drivera02Dev/EE418-FMCW-Radar/SPI/04b_MADV.jpg

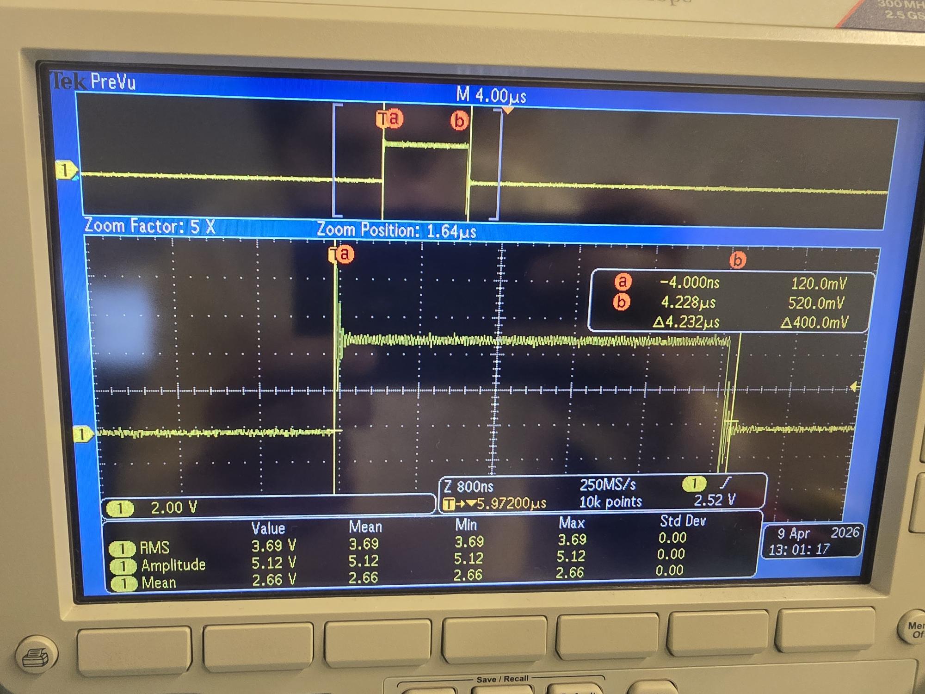
SPI/04b_MADV.jpg
