drivera02Dev/EE418-FMCW-Radar/SPI/Read_1.jpg

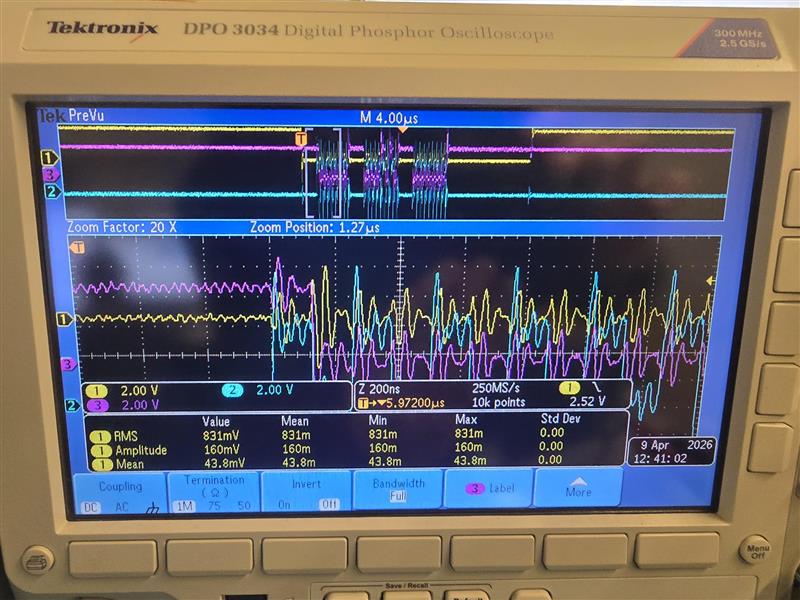
SPI/Read_1.jpg
