drivera02Dev/EE418-FMCW-Radar/SPI/Read_2.jpg

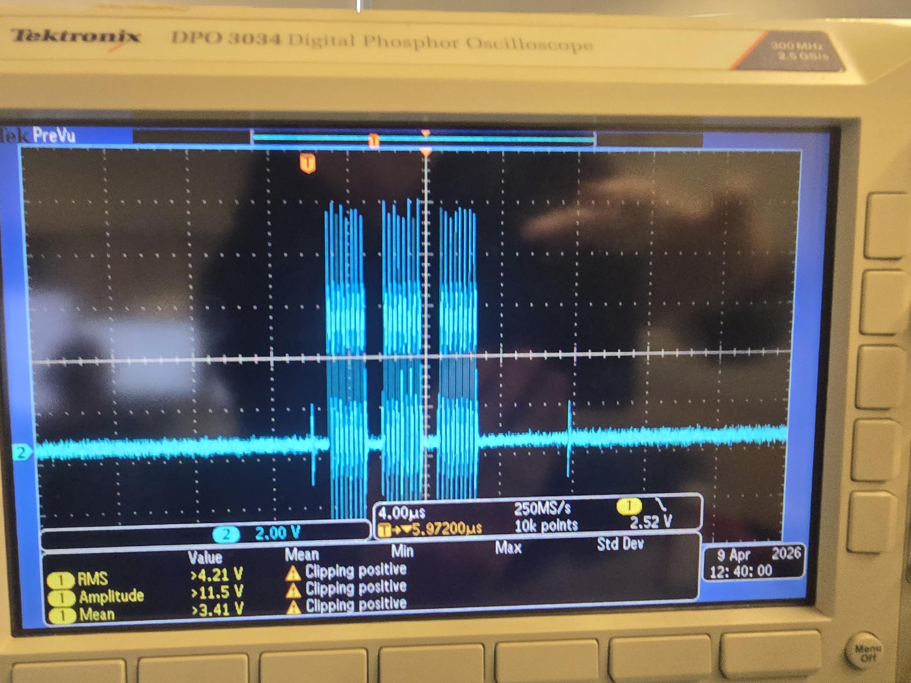
SPI/Read_2.jpg
