drivera02Dev/EE418-FMCW-Radar/SPI/Read_3.jpg

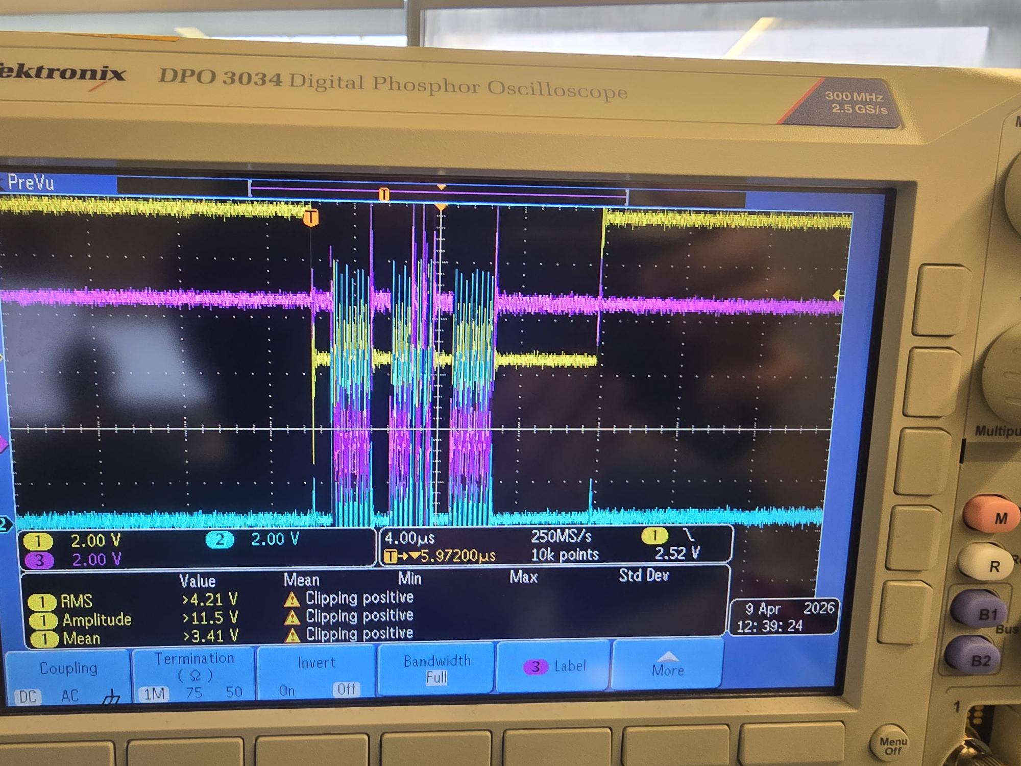
SPI/Read_3.jpg
