drivera02Dev/EE418-FMCW-Radar/SPI/Read_5.jpg

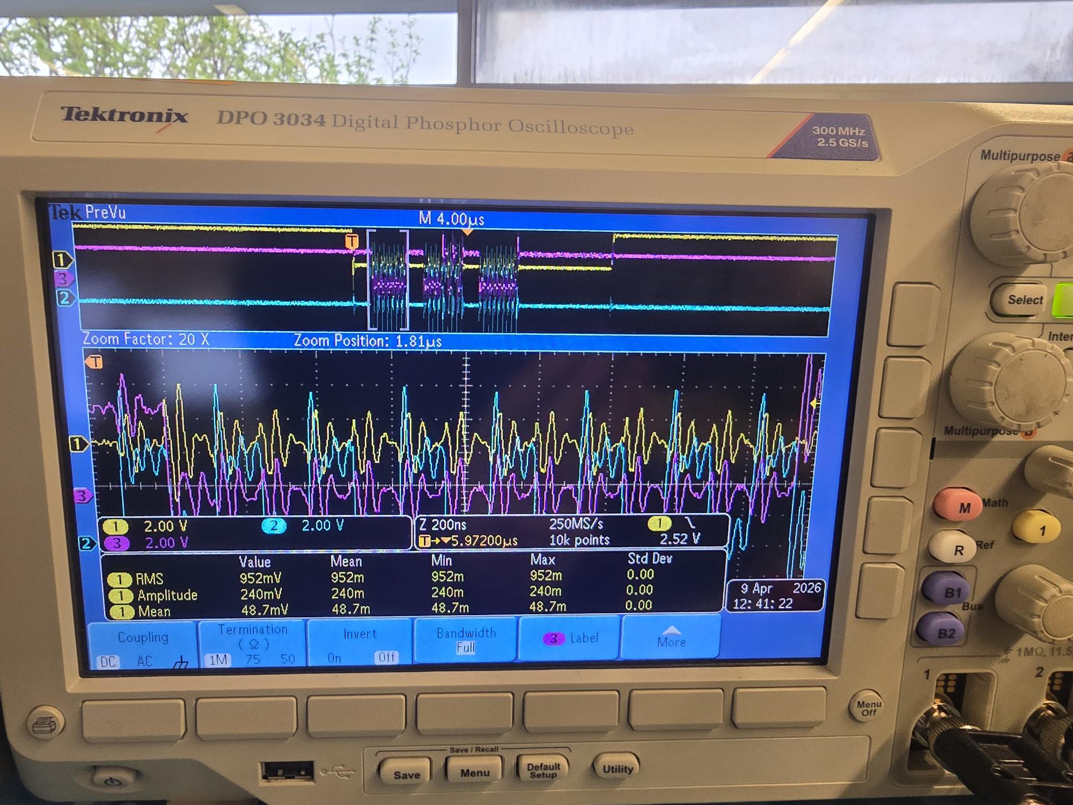
SPI/Read_5.jpg
