drivera02Dev/EE418-FMCW-Radar/SPI/Read_6.jpg

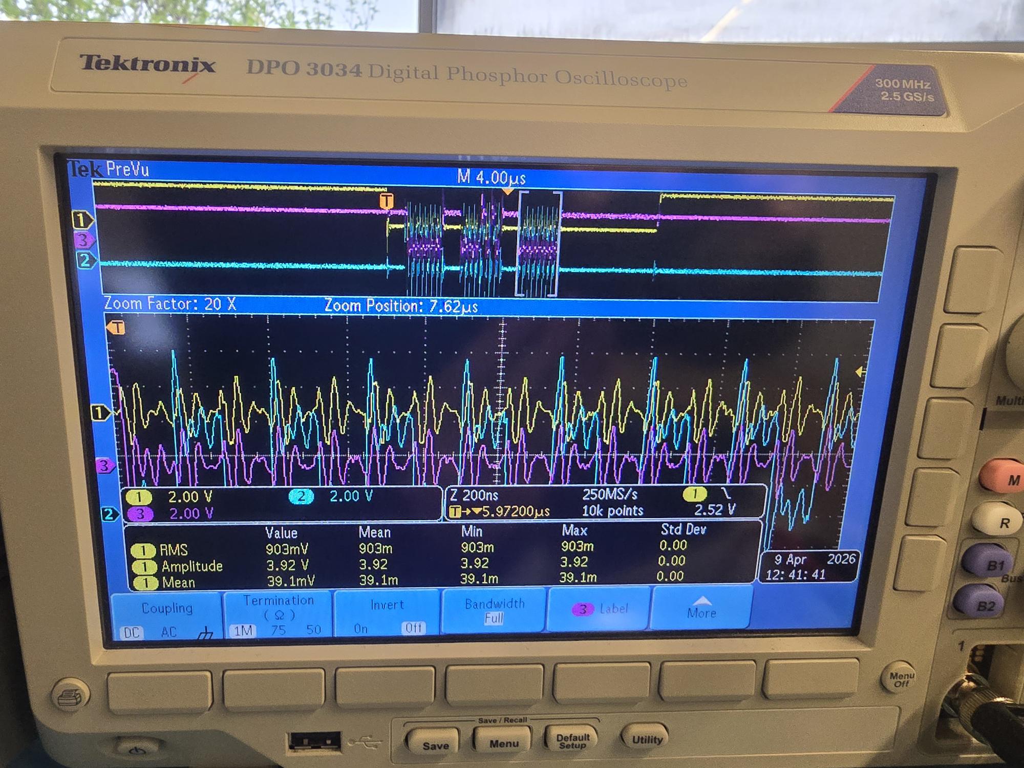
SPI/Read_6.jpg
