drivera02Dev/EE418-FMCW-Radar/SPI/Read_7.jpg

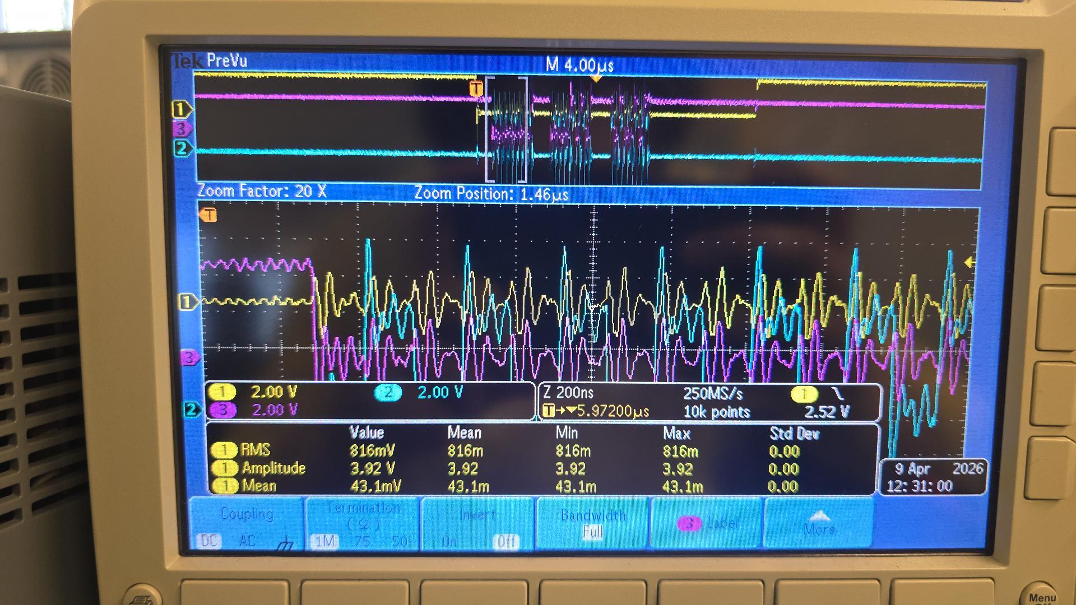
SPI/Read_7.jpg
