drivera02Dev/EE418-FMCW-Radar/SPI/Reference_1.jpg

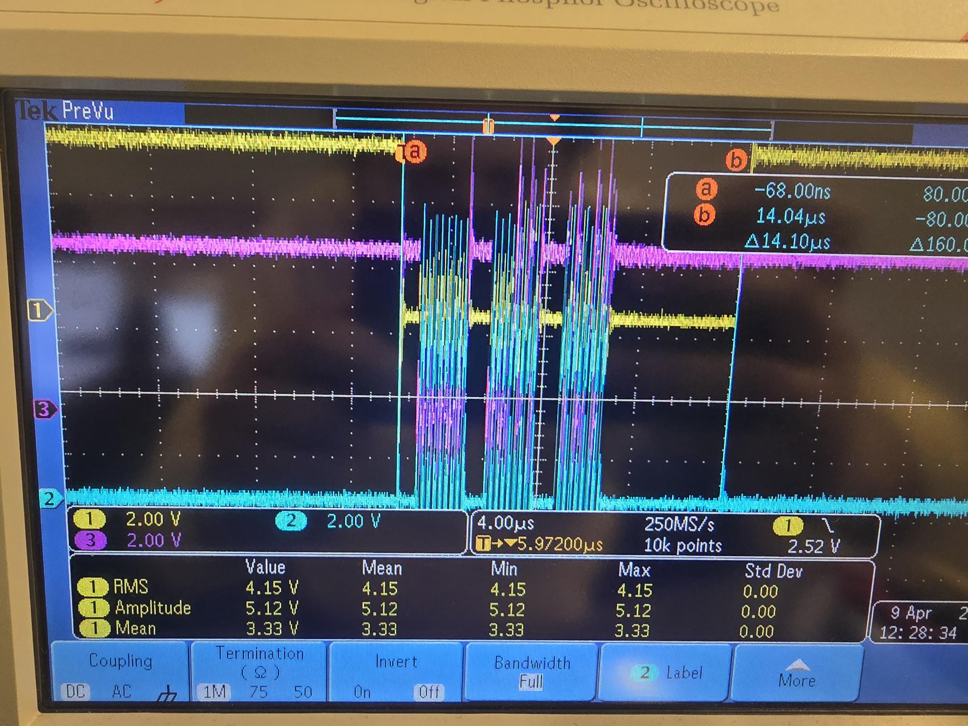
SPI/Reference_1.jpg
