drivera02Dev/EE418-FMCW-Radar/SPI/Reference_2.jpg

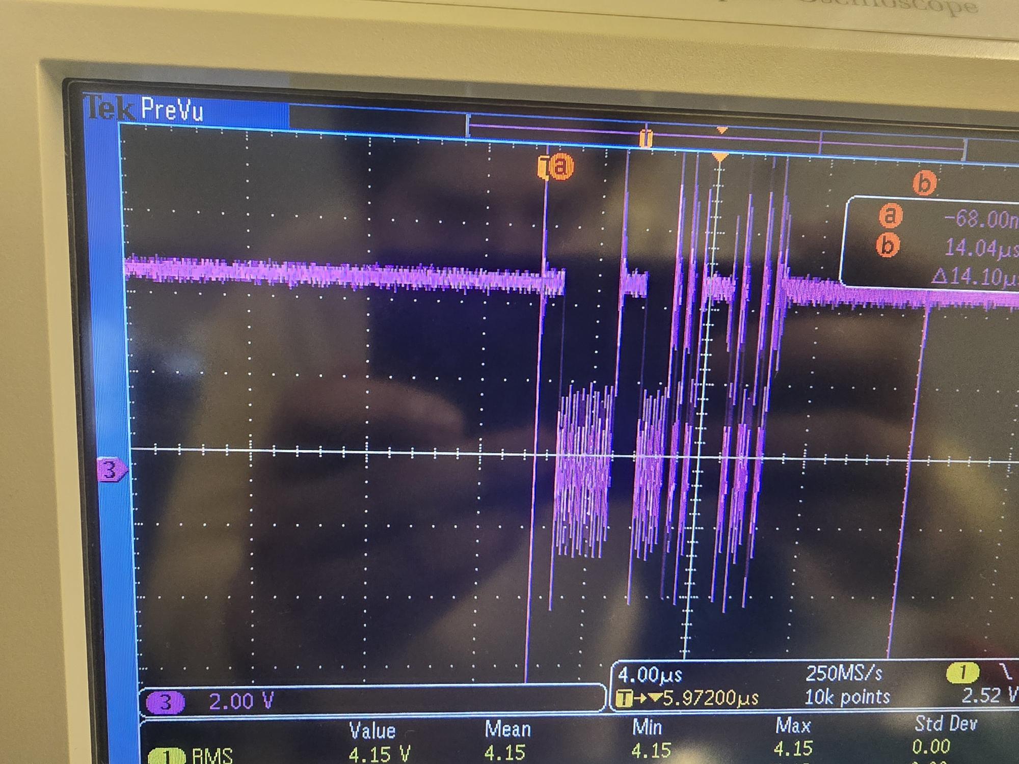
SPI/Reference_2.jpg
