drivera02Dev/EE418-FMCW-Radar/SPI/Reference_3.jpg

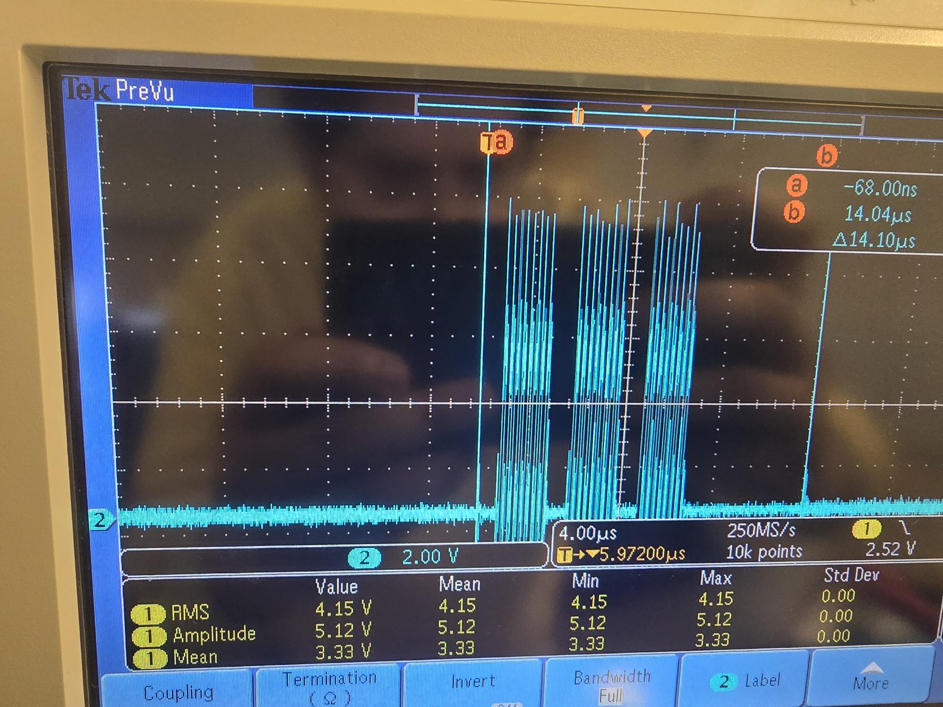
SPI/Reference_3.jpg
