drivera02Dev/EE418-FMCW-Radar/SPI/Reference_5.jpg

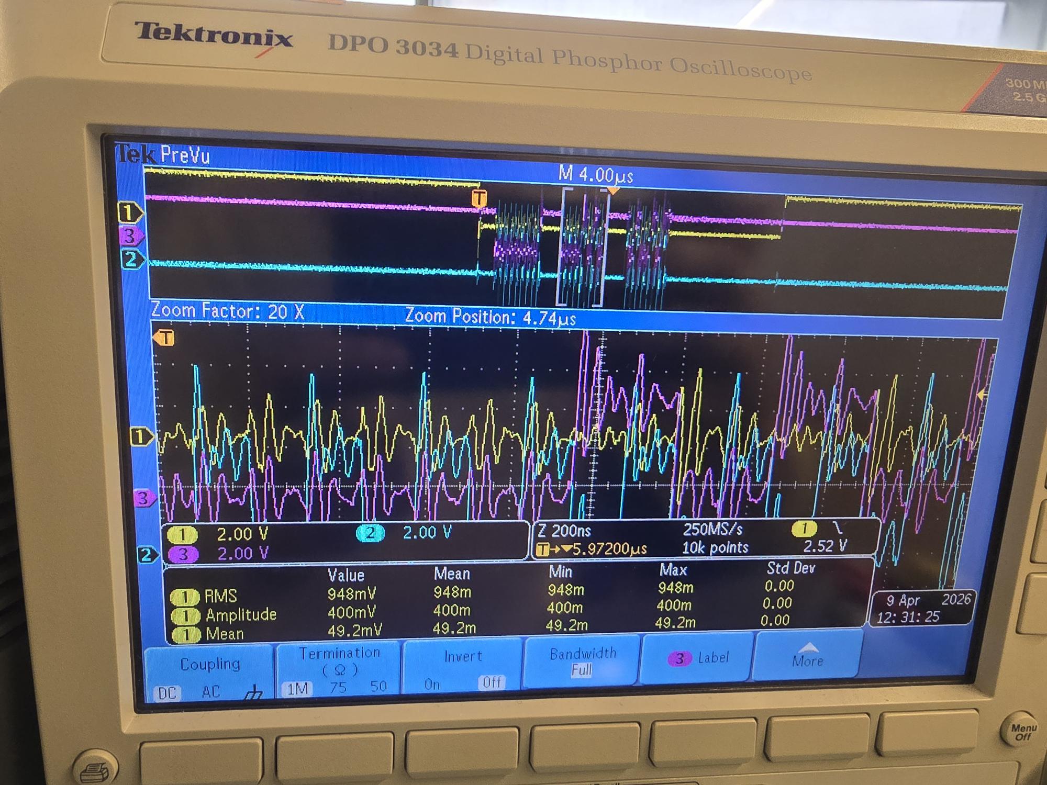
SPI/Reference_5.jpg
