drivera02Dev/EE418-FMCW-Radar/SPI/Reference_6.jpg

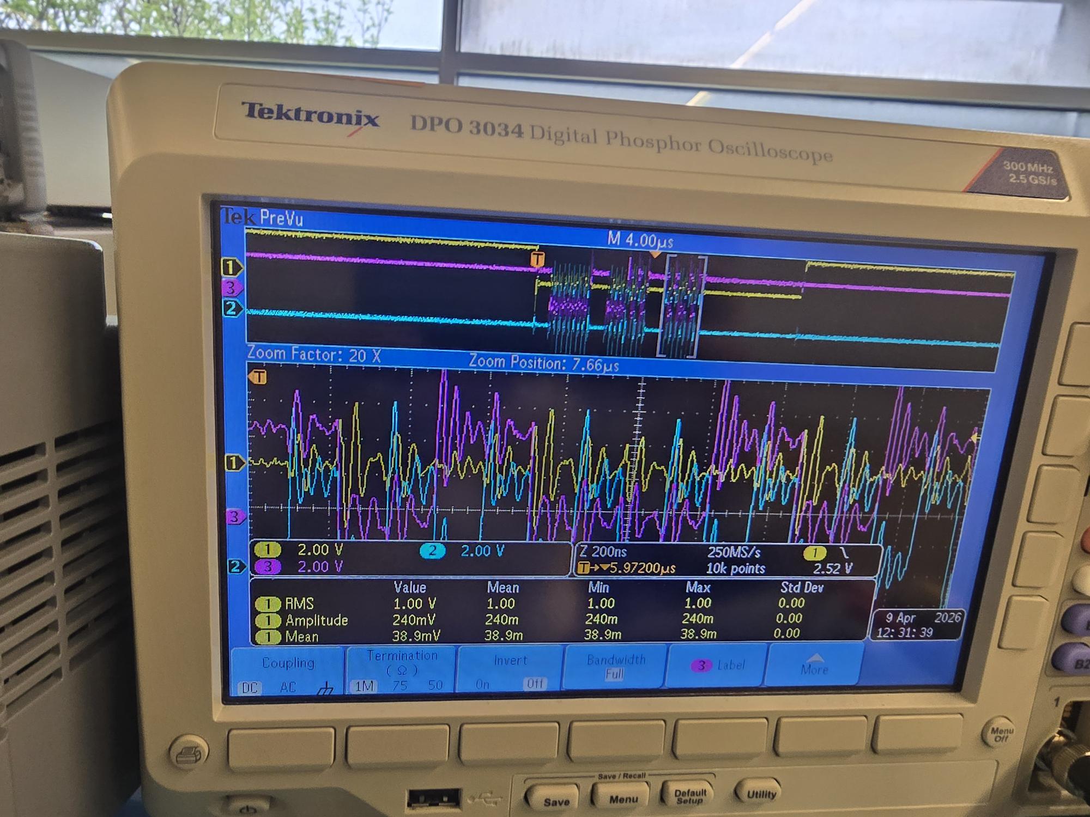
SPI/Reference_6.jpg
