drivera02Dev/EE418-FMCW-Radar/SPI/Reset_1.jpg

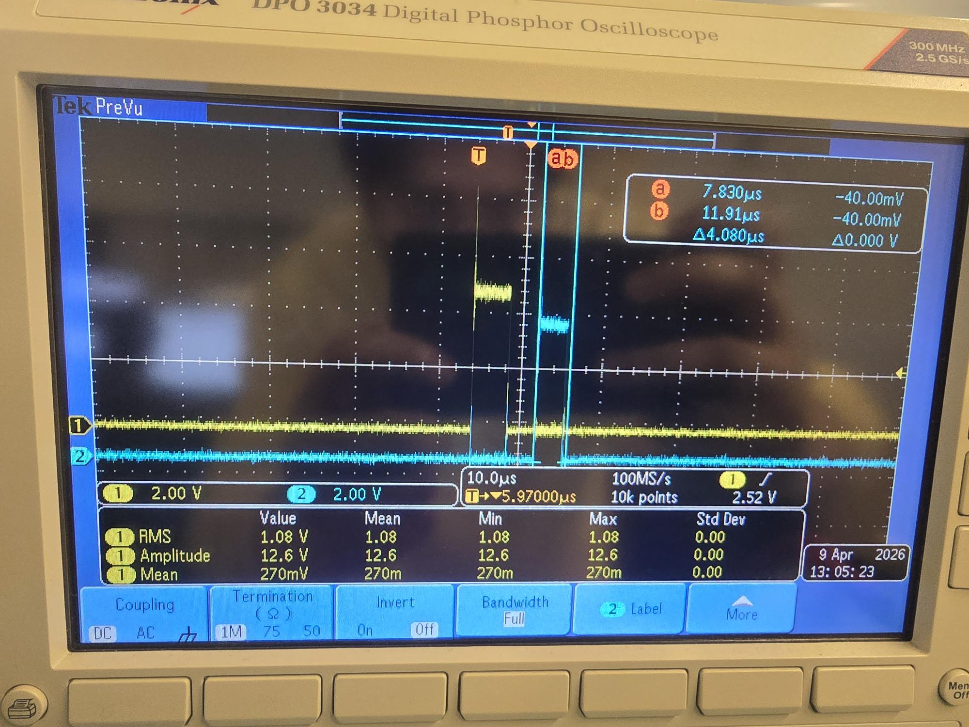
SPI/Reset_1.jpg
