drivera02Dev/EE418-FMCW-Radar/SPI/Reset_3.jpg

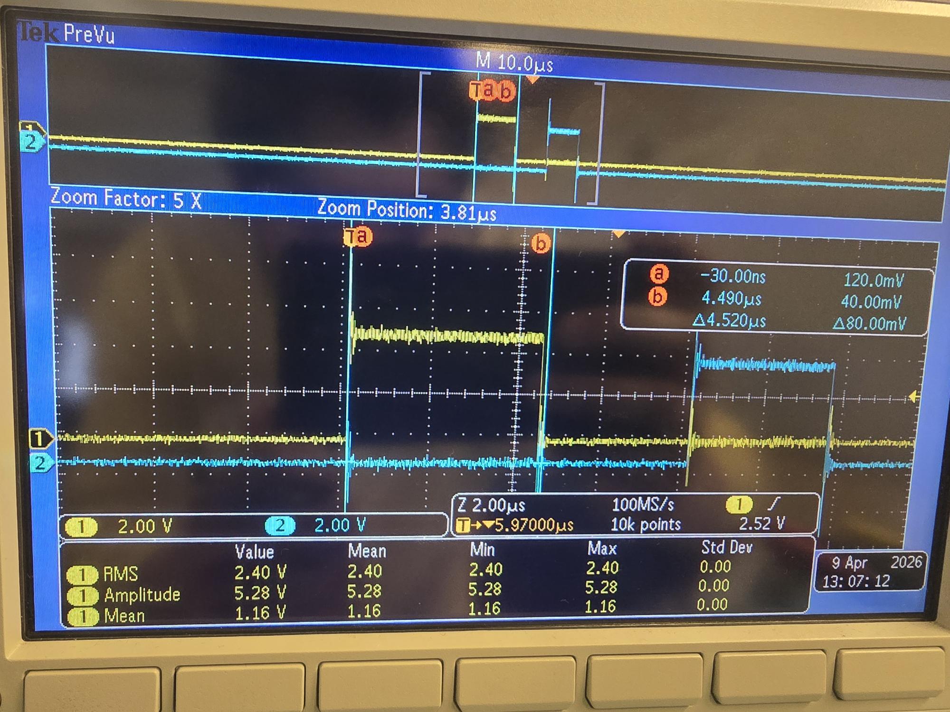
SPI/Reset_3.jpg
