drivera02Dev/EE418-FMCW-Radar/SPI/Reset_4.jpg

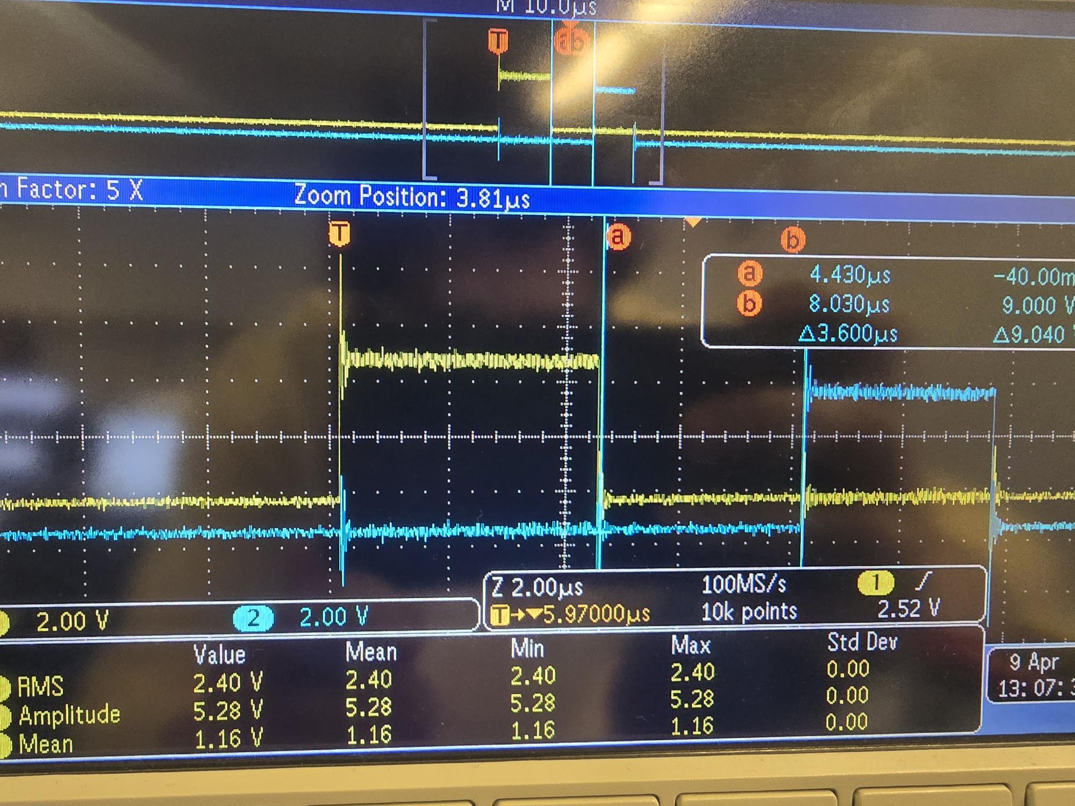
SPI/Reset_4.jpg
