drivera02Dev/EE418-FMCW-Radar/SPI/shared image (1).jpg

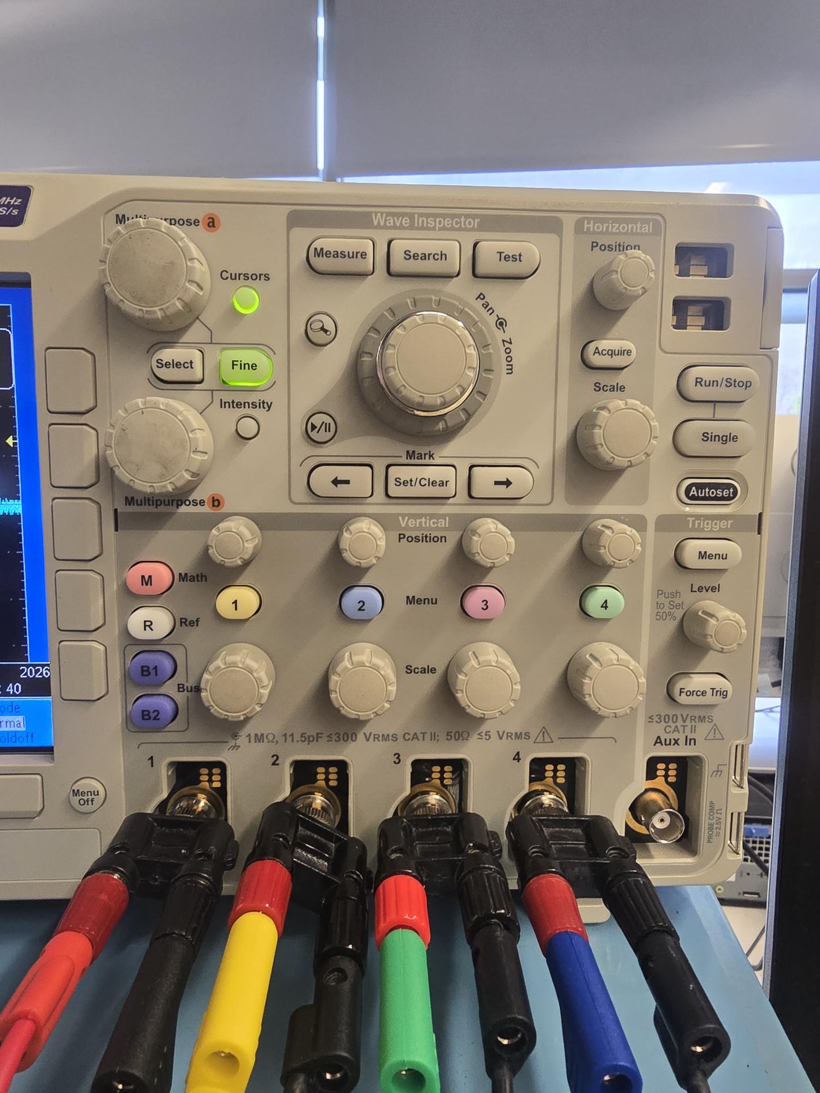
SPI/shared image (1).jpg
