drivera02Dev/EE418-FMCW-Radar/SPI/shared image (2).jpg

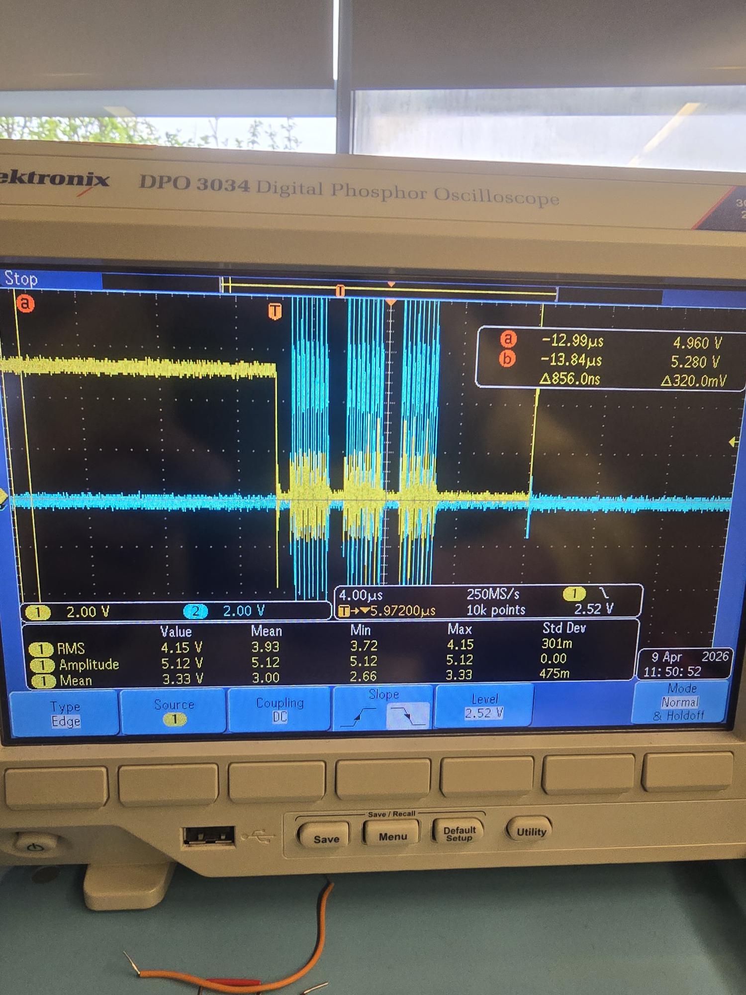
SPI/shared image (2).jpg
