drivera02Dev/EE418-FMCW-Radar/SPI/shared image (3).jpg

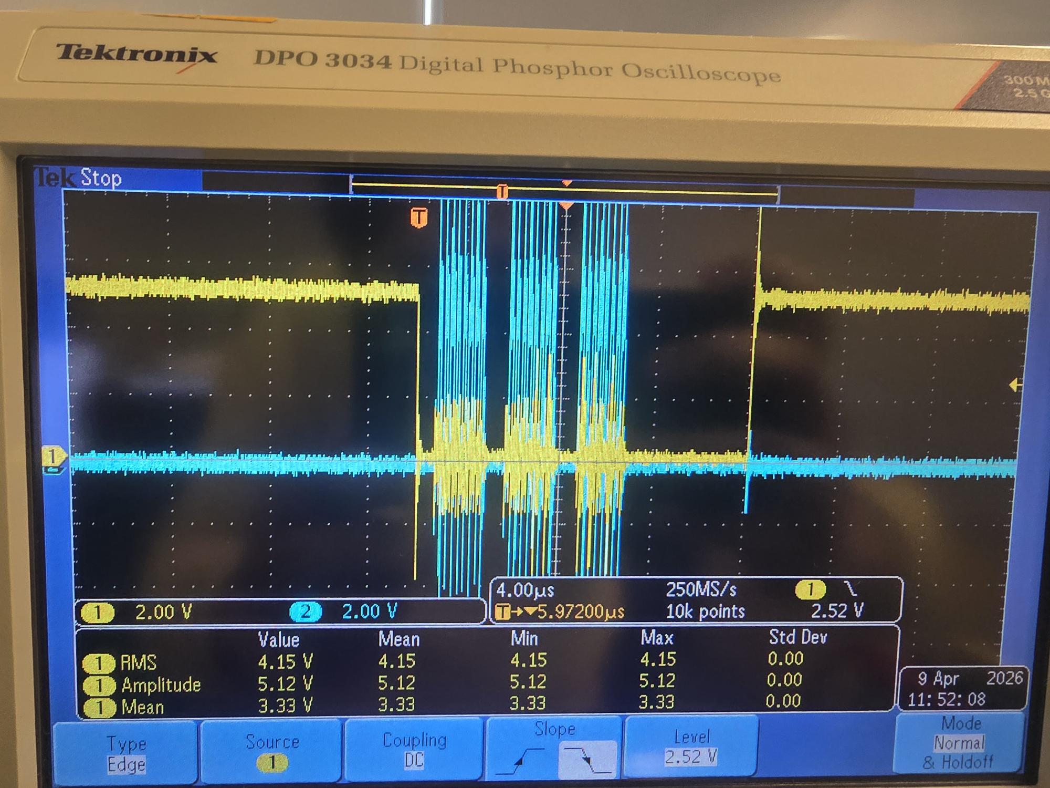
SPI/shared image (3).jpg
