drivera02Dev/EE418-FMCW-Radar/SPI/shared image (4).jpg

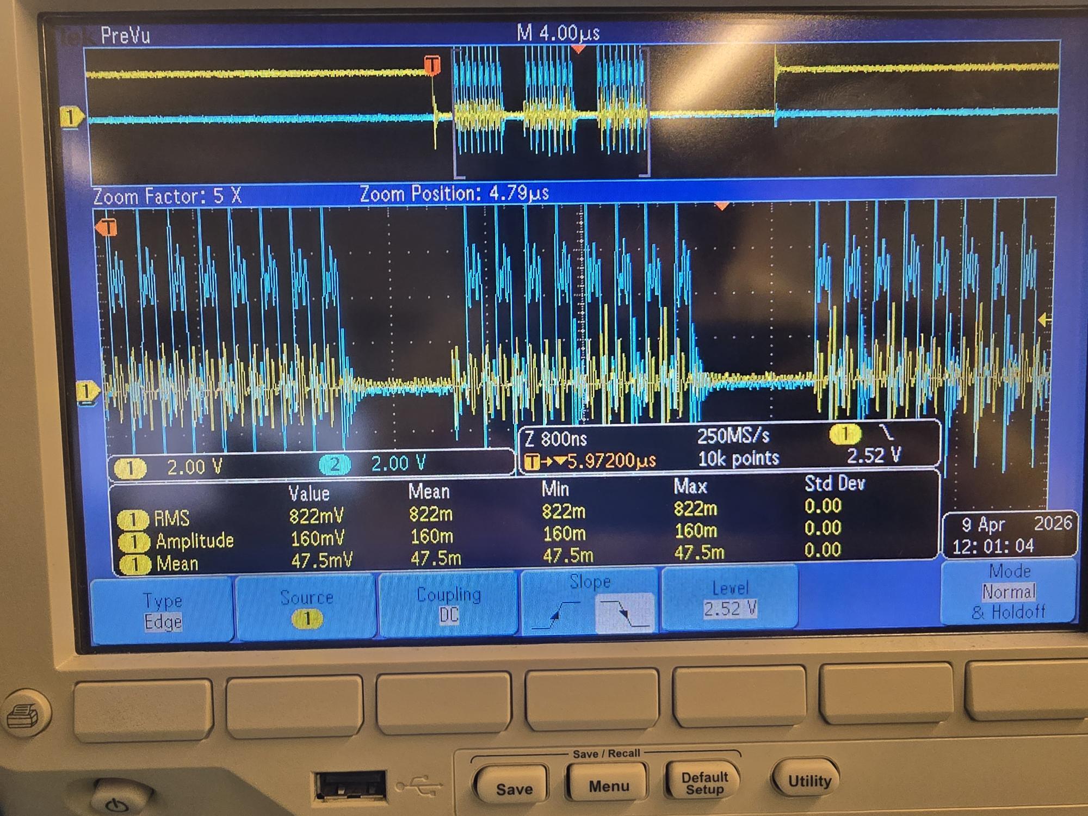
SPI/shared image (4).jpg
