drivera02Dev/EE418-FMCW-Radar/SPI/shared image (5).jpg

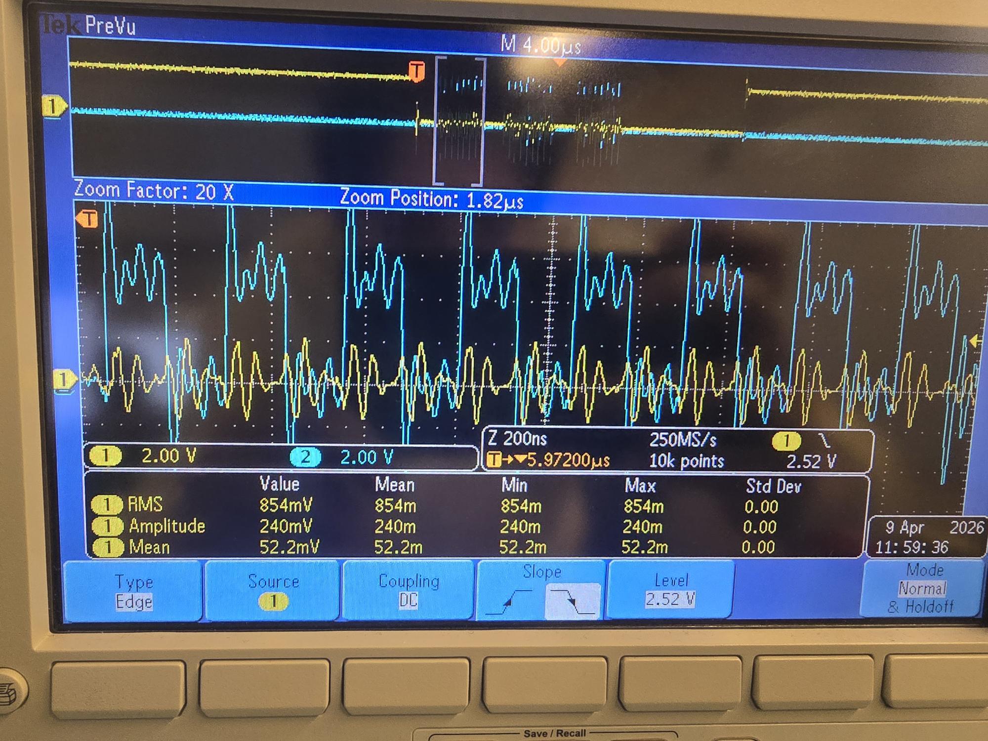
SPI/shared image (5).jpg
