drivera02Dev/EE418-FMCW-Radar/SPI/shared image (8).jpg

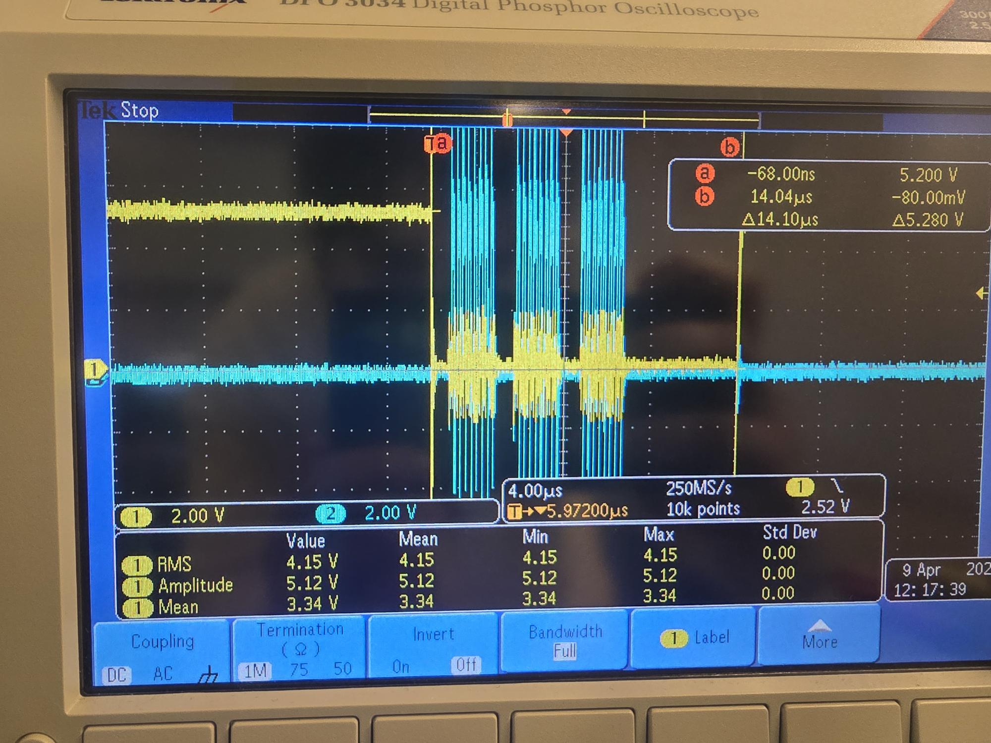
SPI/shared image (8).jpg
