drivera02Dev/EE418-FMCW-Radar/SPI/shared image.jpg

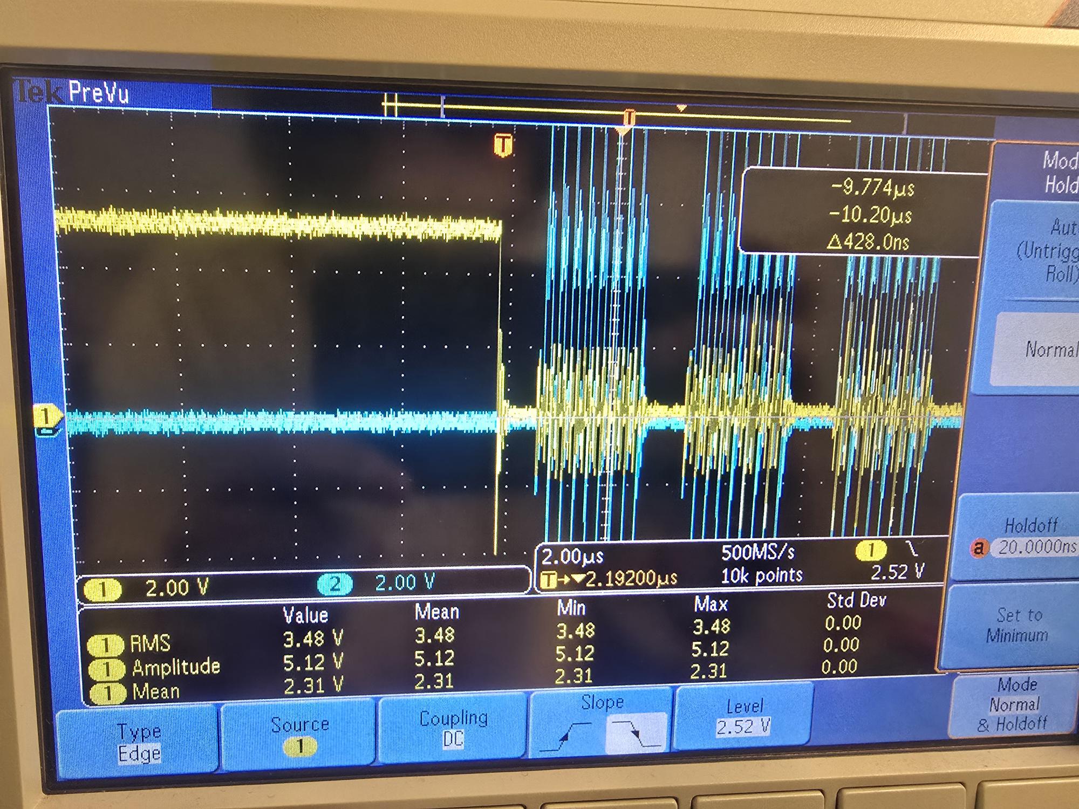
SPI/shared image.jpg
